nobomi/Arduino-ARMSID-configurator/Arduino/ARMSID_test/ARMSID_test.ino

/*
** ArmSID & Arm2SID tester/configurator using cc65 or Borland Turbo C++ V1.0. or Arduino and others
**
** Copyright (c) 2021 nobomi (Bohumil Novacek, dzin@post.cz)
**
** MIT License
**
** Permission is hereby granted, free of charge, to any person obtaining a copy
** of this software and associated documentation files (the "Software"), to deal
** in the Software without restriction, including without limitation the rights
** to use, copy, modify, merge, publish, distribute, sublicense, and/or sell
** copies of the Software, and to permit persons to whom the Software is
** furnished to do so, subject to the following conditions:
**
** The above copyright notice and this permission notice shall be included in all
** copies or substantial portions of the Software.
**
** THE SOFTWARE IS PROVIDED "AS IS", WITHOUT WARRANTY OF ANY KIND, EXPRESS OR
** IMPLIED, INCLUDING BUT NOT LIMITED TO THE WARRANTIES OF MERCHANTABILITY,
** FITNESS FOR A PARTICULAR PURPOSE AND NONINFRINGEMENT. IN NO EVENT SHALL THE
** AUTHORS OR COPYRIGHT HOLDERS BE LIABLE FOR ANY CLAIM, DAMAGES OR OTHER
** LIABILITY, WHETHER IN AN ACTION OF CONTRACT, TORT OR OTHERWISE, ARISING FROM,
** OUT OF OR IN CONNECTION WITH THE SOFTWARE OR THE USE OR OTHER DEALINGS IN THE
** SOFTWARE.
*/

#include "sidapi.h"

/*****************************************************************************/
/*                                   Data                                    */
/*****************************************************************************/

#ifdef ARM2SID
#define Nadpis "\\\\       nobomi armsid tester v3.16\\\\\\"
#else
#define Nadpis "\\\\       nobomi armsid tester v2.16\\\\\\"
#endif
#define Notfou "armsid not found"
#ifdef ARM2SID
#define Founda_0 "armsid"
#define Founda_1 "arm2sid  left channel"
#define Founda_2 "arm2sid right channel"
#else
#define Founda "armsid"
#endif

#define WarnBL      "!! warning ! bootloader fw  ! warning !!"
#define WarnBeta "!! warning ! beta firmware  ! warning !!"

/*****************************************************************************/
/*                                   Code                                    */
/*****************************************************************************/

static unsigned char SIDi;
static unsigned char version;
static unsigned char revision;
static unsigned char release;

struct s_vyber_list {
  const unsigned char left;
  const unsigned char top;
  const signed char rozsah;
};

typedef struct {
  unsigned char *vyber;
  const struct s_vyber_list *list;
  signed char *value;
} t_vyber;

static unsigned char vyber;
static unsigned char vyber_max;
signed char vyber_value[5];
signed char vyber_mask=0;
static const struct s_vyber_list extend_lists[4]={
  {0,4,7},
  {0,8,1},
  {0,12,3},
  {0,16,3}
};

#ifdef DIGIFIX
#define audio_value vyber_value
static const struct s_vyber_list audio_lists[2]={
  {0,9,0},
  {0,14,4},
};
static signed char audio_mem[4];
static unsigned char isext;
#endif

#ifdef ARM2SID
static unsigned char mem_value[8];
static unsigned char isARM2;
static unsigned char mem_emul;
static unsigned char ntsc;
static unsigned char downM;
static unsigned char socket;

#define EMUL_SID    0
#define EMUL_SFX    1
#define EMUL_SFX_SID  2

#define ADDR_MAP_NONE   0
#define ADDR_MAP_SIDL   1
#define ADDR_MAP_SIDR   2
#define ADDR_MAP_SFX    3
#define ADDR_MAP_SIDM   4

#define ADDR_MAP_D400   0
#define ADDR_MAP_D420   1
#define ADDR_MAP_D500   2
#define ADDR_MAP_D520   3
#define ADDR_MAP_DE00   4
#define ADDR_MAP_DE20   5
#define ADDR_MAP_DF00   6
#define ADDR_MAP_DF20   7
#endif

#define EXTIN_NO      0
#define EXTIN_YES     CHAR_E

#define DIGIFIX_NO        0
#define DIGIFIX_YES        0x58

char get_p(void) {
  return SIDrd(27);
}

char get_q(void) {
  return SIDrd(28);
}

//sending command
void send_cmd(char x31, char x30) {
  SIDwr(31, x31);
  SIDwr(30, x30);
}

//plus wait 10ms
void send_cmd_wait(char x31, char x30) {
  send_cmd(x31,x30);
  delay(10);
}

//sending config command and reading half of the two-byte output
char get_pcmd(char x31, char x30) {
  send_cmd(x31,x30);
  delay(1);
  return get_p();
}

//close the config mode
void sid_off(void) {
  SIDwr(29, 0);
  SIDwr(29, 0);
  SIDwr(29, 0);
}

//open the config mode
void sidoffon(void) {
  sid_off();
  delay(10);
  send_cmd(CHAR_D, CHAR_I);
  SIDwr(29, CHAR_S);
  delay(1);
}

void textcolorLB(void) {
  textcolor(COLOR_LIGHTBLUE);
}

void textcolorW(void) {
  textcolor(COLOR_WHITE);
}

//print char as a decimal
void cputbval(unsigned char x) {
  char sto=0;
  char deset=0;
  if (x>=100) {
    do {
      x-=100;sto++;
    } while (x>=100);
    cputc(sto+'0');
  }
  while (x>=10) {
    x-=10;deset++;
  }
  if (sto|deset) cputc(deset+'0');
  cputc(x+'0');
}

//print short as a 1/1000 decimal
void cput1000(unsigned short x) {
  char t=0;
  char m;
  while (x>=1000) {
    x-=1000;t++;
  }
  cputbval(t);
  cputc('.');
  t='0';while (x>=100) { x-=100;t++; } cputc(t);
  m=x;
  t='0';while (m>=10) { m-=10;t++; } cputc(t);
  cputc(m+'0');
}

//drawing acceleration, x,y = position, znak=character, kolik=number of characters, if negative then characters are in a column
struct s_canvas {
  unsigned char x;
  unsigned char y;
  unsigned char znak;
  signed char kolik;
} t_canvas;

//frame clearing
static const struct s_canvas prazdny_ramecek[]={
  {0,0,' ',40},
  {0,1,' ',-3},
  {39,1,' ',-3},
  {0,4,' ',40},
  {0,0,0,0}
};

//frame
static const struct s_canvas plny_ramecek[]={
// PC double lines
  {0, 0,  CHAR_FRAME_TOP_LEFT,      1 },
  {1, 0,  CHAR_FRAME_TOP,           38},
  {39,0,  CHAR_FRAME_TOP_RIGHT,     1 },
  {0, 1,  CHAR_FRAME_LEFT,          -3},
  {39,1,  CHAR_FRAME_RIGHT,         -3},
  {0, 4,  CHAR_FRAME_BOTTOM_LEFT,   1 },
  {1, 4,  CHAR_FRAME_BOTTOM,        38},
  {39,4,  CHAR_FRAME_BOTTOM_RIGHT,  1 },
  {0, 0,  0,                        0 }
};

//one line
static const struct s_canvas lajna[]={
  {2,2,CHAR_LINE,36},
  {0,0,0,0}
};

//automaton for drawing acceleration structures, x0,y0 = position offset
void namaluj(unsigned char x0, unsigned char y0, const struct s_canvas *c) {
  while (c->znak) {
    signed char i=c->kolik;
    if (i<0) {
      while (++i<=0) {
        gotoxy(x0+c->x,y0+c->y-i);
        cputc(c->znak);
      }
    } else {
      gotoxy(x0+c->x,y0+c->y);
      while (i) { cputc(c->znak);i--; }
    }
    c++;
  }
}

void candidate() {
    if (release) {
        char x=wherex();
        char y=wherey();
    (void) bordercolor(COLOR_YELLOW);
    (void) textcolor(COLOR_YELLOW);
        revers(1);
        if (release==255) {
            cputs2xy(0,0,WarnBL);
#ifdef TERMINAL_HEIGHT
      cputs2xy(0,TERMINAL_HEIGHT-1,WarnBL);
#else
      cputs2xy(0,24,WarnBL);
#endif
        } else {
      cputs2xy(0,0,WarnBeta);
#ifdef TERMINAL_HEIGHT
      cputs2xy(0,TERMINAL_HEIGHT-1,WarnBeta);
#else
      cputs2xy(0,24,WarnBeta);
#endif
        }
        revers(0);
        //back
    (void) textcolor(COLOR_WHITE);
        gotoxy(x,y);
    }
}

void new_page(void) {
    clrscr();
    candidate();
    cputs2(Nadpis);
}

//print the first page header
void uvod(void) {
    (void) textcolor(COLOR_WHITE);
    (void) bordercolor(COLOR_LIGHTBLUE);
    (void) bgcolor(COLOR_BLUE);
    new_page();
}

//filter setting key reaction
signed char vyber_zmena(const struct s_vyber_list *v, unsigned char key, char ramecek) {
  signed char res=-1;
    if ((key==17)||(key==17+128)) {
    namaluj(v[vyber].left,v[vyber].top,prazdny_ramecek);
    }
    switch (key) {
  case 17:
    //down
    vyber++;if (vyber>=vyber_max) vyber=0;
    break;
  case 17+128:
    //up
    if (vyber>0) vyber--;
    else vyber=vyber_max-1;
    break;
  case 29:
    //right
    if (v[vyber].rozsah) { if (vyber_value[vyber]<v[vyber].rozsah) { vyber_value[vyber]++;res=vyber; }
    } else { vyber_value[vyber]=1; res=vyber; }
    break;
  case 29+128:
    //left
    if (v[vyber].rozsah) { if (vyber_value[vyber]>-v[vyber].rozsah) { vyber_value[vyber]--;res=vyber; }
    } else { vyber_value[vyber]=0;res=vyber; }
    break;
  default:
  break;
    }
    if ((v[vyber].rozsah)&&((vyber_value[vyber]>v[vyber].rozsah)||(vyber_value[vyber]<-v[vyber].rozsah))) { vyber_value[vyber]=0;res=vyber; }
    if (((key==17)||(key==17+128))&&(ramecek)) {
    namaluj(v[vyber].left,v[vyber].top,plny_ramecek);
    }
  namaluj(v[vyber].left,v[vyber].top,lajna);
  if (v[vyber].rozsah) {
      gotoxy(v[vyber].left+19+((17*vyber_value[vyber])/v[vyber].rozsah),v[vyber].top+2);
  } else {
    gotoxy(v[vyber].left+2+34*(vyber_value[vyber]&1),v[vyber].top+2);
  }
    cputc(CHAR_CHOICE_1);
    cputc(CHAR_CHOICE_2);
  return res;
}

//print extended page offer
void save_back_quit(void) {
#ifdef TERMINAL_HEIGHT
  gotoxy(4,TERMINAL_HEIGHT-2);
#else
  gotoxy(4,22);
#endif
  cputs2("@save / @permanently / @back / @quit");
}

//print the filter setting page
void uvod_extend(void) {
    uvod();

    cputs2xy(0+8, 4+1,       "mos 6581 filter strength");

    cputs2xy(0+1, 4+3,"follin galway  average  strong extreme");

    cputs2xy(0+4, 8+1,   "mos 6581 lowest filter frequency");

    cputs2xy(0+1, 8+3," 150             215              310");

    cputs2xy(0+4,12+1,   "mos 8580 filter central frequency");

    cputs2xy(0+1,12+3," 12000           6000            3000");

    cputs2xy(0+4,16+1,   "mos 8580 lowest filter frequency");

    cputs2xy(0+1,16+3," 30              100              330");

    save_back_quit();

    vyber=0;
    vyber_zmena(extend_lists,17,0);
    vyber_zmena(extend_lists,17,0);
    vyber_zmena(extend_lists,17,0);
    vyber_zmena(extend_lists,17,1);
}

//print nibble as a hex value
void cputnibble(unsigned char x) {
  x&=15;
  if(x>9) x=('a'-10)+x;
  else x+='0';
  cputc(x);
}

//print short as a hex value
void cputhex_mem(unsigned short x) {
  cputc('$');
  cputnibble(x>>12);
  cputnibble(x>>8);
  cputnibble(x>>4);
  cputnibble(x);
}

#ifdef SOCKETS_NAMED
void cputhex(unsigned short x) {
  cputs2("socket ");
  if (x&0x3FF) cputc('2');
  else cputc('1');
}
#else
void cputhex(unsigned short x) {
  cputhex_mem(x);
}
#endif

//saving configuration to the ram or permanently to the flash memory of ARMSID
void save(char jak) {
    char i;
    clrscr();
    uvod();
    switch(jak) {
  case 's':
      gotoxy(13,12);
      cputs2("saving to ram");
    send_cmd(0xC0,CHAR_E);
      gotoxy(13,13);
      for(i=0;i<13;i++) {
    delay(1000/13);
    cputc('#');
      }
  break;
  case 'p':
      gotoxy(12,12);
      cputs2("saving to flash");
    send_cmd(0xCF,CHAR_E);
      gotoxy(12,13);
      for(i=0;i<15;i++) {
    delay(2000/15);
    cputc('#');
      }
  break;
  default:break;
    }
}

#ifdef ARM2SID
//update memory mapping page with item x highlighted
void vyber_mem(char x) {
  char i;
  char is3=((mem_value[1]==ADDR_MAP_SIDM)||(mem_value[2]==ADDR_MAP_SIDM))&&(!socket);
  for(i=0;i<8;i++) {
      gotoxy(5+((i>>2)?18:0),8+((i&3)<<1));
      if (socket) {
      if (i&3) textcolor(COLOR_BLUE);
      if (i&4) cputs2("sid/2:");
      else cputs2("sid/1:");
      textcolorW();
    } else {
      cputhex_mem((int)SIDgetaddr(i));
      cputc(':');
    }
  }
  for(i=0;i<8;i++) {
      gotoxy(5+7+((i>>2)?18:0),8+((i&3)<<1));
      if (x==i) revers(1);
      if (socket) {
      if (i&3) {
        textcolor(COLOR_BLUE);
        cputs2("none");
        goto vyber_dalsi;
      }
    }
    if ((mem_emul==EMUL_SFX_SID)&&(i<(socket?4:6))) {
      if (i==0) {
        cputs2("sidl");
      } else {
        cputs2("Lnone");
      }
    } else if ((i>=(socket?4:6))&&(mem_emul>=EMUL_SFX)) cputs2("sfx ");
      else switch (mem_value[i]) {
      case ADDR_MAP_SFX:
        if (mem_emul==EMUL_SFX) textcolorLB();
        cputs2("sfx ");
        break;
      case ADDR_MAP_SIDL:
        if (mem_emul==EMUL_SFX) textcolorLB();
        cputs2("sidl");
        break;
      case ADDR_MAP_SIDR:
        if (mem_emul==EMUL_SFX) textcolorLB();
        if ((mem_emul==EMUL_SID)||(i>0)) cputs2("sidr");
        else cputs2("sidl");
        break;
      case ADDR_MAP_SIDM:
        if (mem_emul==EMUL_SFX) textcolorLB();
        else if (mem_emul==EMUL_SID) textcolor(COLOR_LIGHTGREEN);
        if ((mem_emul==EMUL_SID)||(i>0)) cputs2("sid3");
        else cputs2("sidl");
        break;
      case ADDR_MAP_NONE:
      default:
          if (x!=i) textcolorLB();
        cputs2("none");
        break;
    }
vyber_dalsi:
    textcolorW();
      if (x==i) revers(0);
  }
    gotoxy(4+18,16);
  if (!is3) cputc(' ');
  textcolorLB();
  if (mem_emul==EMUL_SFX_SID) {
    if (is3) { cputc(' '); }
    cputs2("sid sfx ");
    if (x==8) revers(1);
    cputs2("WbothR");
  } else if (mem_emul==EMUL_SFX) {
    if (is3) { cputc(' '); }
    cputs2("sid ");
    if (x==8) revers(1);
    cputs2("WsfxR LbothW");
  } else {
    if (x==8) revers(1);
    if (is3) { textcolor(COLOR_LIGHTGREEN);cputc('3'); }
    cputs2("WsidR Lsfx bothW");
  }
  //pal ntsc
  gotoxy(5+18,18);
  if (mem_emul==EMUL_SID) {
    cputs2("Lpal ntscW");
  } else {
    if (ntsc) {
      cputs2("Lpal W");
      if (x==9) revers(1);
      cputs2("ntscR");
    } else {
      if (x==9) revers(1);
      cputs2("palRL ntscW");
    }
  }
  //mono
  gotoxy(5+18,20);
  if (mem_emul==EMUL_SFX) {
    cputs2("Loff onW");
  } else {
    if (downM) {
      cputs2("Loff W");
      if (x==10) revers(1);
      cputs2("onR");
    } else {
      if (x==10) revers(1);
      cputs2("offRL onW");
    }
  }
  //socket
  gotoxy(5+18,6);
    if (socket) {
      cputs2("Lwire W");
      if (x==11) revers(1);
      cputs2("socketR");
    } else {
      if (x==11) revers(1);
      cputs2("wireRL socketW");
    }
}

static const char socket_next[12]={0,4,2,0,4,8,6,4,8,9,10,11};

//memory mapping key reaction
void mem_zmena(unsigned char key) {
  char vyber_old=vyber;
    switch (key) {
  case 17:
    //down
    vyber++;if (vyber>11) vyber=0;
    if ((vyber==9)&&(mem_emul==0)) vyber=10;
    if ((vyber==10)&&(mem_emul==1)) vyber=11;
    if ((mem_emul>=EMUL_SFX)&&(vyber<8)) vyber=8;
    break;
  case 17+128:
    //up
    if (vyber>0) vyber--;
    else vyber=11;
    if ((mem_emul>=EMUL_SFX)&&(vyber<8)) vyber=11;
    if ((vyber==10)&&(mem_emul==1)) vyber=9;
    if ((vyber==9)&&(mem_emul==0)) vyber=8;
    break;
  case 29:
    //right
    if (vyber==11) {
      socket^=1;
    } else if (vyber==10) {
      downM^=1;
    } else if (vyber==9) {
      ntsc^=4;
    } else if (vyber==8) {
      mem_emul++;//=(mem_emul+1)%3;
      if (mem_emul>=3) mem_emul=0;
    } else {
      mem_value[vyber]++;
      if (mem_value[vyber]>4) mem_value[vyber]=0;
      else if (mem_value[vyber]>2) {
        if (vyber==0) mem_value[vyber]=1;
        else {
          if ((vyber==1)||(vyber==2)) mem_value[vyber]=4; //enable for D420 a D500
          else mem_value[vyber]=0;
        }
      }
    }
    break;
  case 29+128:
    //left
    if (vyber==11) {
      socket^=1;
    } else if (vyber==10) {
      downM^=1;
    } else if (vyber==9) {
      ntsc^=4;
    } else if (vyber==8) {
      mem_emul+=2;
      if (mem_emul>=3) mem_emul-=3;
    }
    else {
      if (mem_value[vyber]==0) {
        if ((vyber==0)||(vyber>2)) mem_value[vyber]=2;  //povolit jen pro D420 a D500
        else mem_value[vyber]=4;
      }
      else if (mem_value[vyber]==4) mem_value[vyber]=2;
      else mem_value[vyber]--;
      if ((vyber==0)&&(mem_value[vyber]==0)) mem_value[vyber]=2;
    }
    break;
  default:
  break;
    }
    if (vyber_old!=vyber) {
    vyber_mem(-1);
    if (socket) vyber=socket_next[vyber];
  }
    vyber_mem(vyber);
}

//print memory mapping page
void uvod_mem(void) {
    uvod();
    gotoxy(5,3);
    cputs2("address mapping configuration");
    gotoxy(5,6);
    cputs2("pin connections:");
    gotoxy(5,16);
    cputs2("emulation mode: ");
    gotoxy(5,18);
    cputs2("fm frequency ref:");
    gotoxy(5,20);
    cputs2("down-mix to mono:");
  save_back_quit();
  vyber=8;
  vyber_mem(vyber);
}

//memory mapping reading
void nacti_mem(void) {
    unsigned char p,q;
  p=get_pcmd(CHAR_M,CHAR_M);
    q=get_q();
    mem_emul=p&7;
    if (mem_emul&4) ntsc=4; else ntsc=0;
    if ((mem_emul&3)==3) mem_emul=1;
    mem_emul&=3;
  p=get_pcmd(CHAR_X,CHAR_M);
    q=get_q();
    downM=p&1;
    socket=q&1;
    delay(10);
  p=get_pcmd(CHAR_L,CHAR_M);
    q=get_q();
    mem_value[0]=p&15;
    mem_value[1]=p>>4;
    mem_value[2]=q&15;
    mem_value[3]=q>>4;
    delay(10);
  p=get_pcmd(CHAR_H,CHAR_M);
    q=get_q();
    mem_value[4]=p&15;
    mem_value[5]=p>>4;
    mem_value[6]=q&15;
    mem_value[7]=q>>4;
#ifdef DEMO
  mem_value[0]=1;
  mem_value[1]=2;
  mem_value[2]=2;
  mem_value[3]=1;
  mem_value[4]=0;
  mem_value[5]=0;
  mem_value[6]=0;
  mem_value[7]=0;
  ntsc=0;
  socket=0;
  mem_emul=0;
  downM=0;
#endif
}

//memory mapping page automaton
char mem(void) {
    unsigned char key;
    uvod_mem();
    while (1) {
      if (keypressed()) {
      key=cgetc();
      if ((key=='q')||(key=='b')) return key;
      if ((key=='s')||(key=='p')) {
        send_cmd_wait('0'+(mem_emul)+((mem_emul)?(ntsc):0),CHAR_M);
        send_cmd_wait(((downM)?CHAR_R:CHAR_S),CHAR_M);
        send_cmd_wait(((socket)?CHAR_E:CHAR_C),CHAR_M);
        {
          unsigned char i=0;
          while (i<8) {
            send_cmd_wait(0x80|(i<<4)|(mem_value[i]&15),CHAR_M);
            i++;
          }
        }
      }
      if (key=='s') {
      save(key);
      return 'r';
      }
      if (key=='p') {
      save(key);
      return 'r';
      }
        mem_zmena(key);
    }
    }
}

//ARM2SID testing => if answer to command "SII" is L or R then it's ARM2SID otherwise it's ARMSID
char test_lr(char x) {
#ifdef DEMO
  SIDaddr=(SIDaddrtype)(SIDgetaddr(x));SIDi=x;
  isARM2=1;return (x+1)%3;
#else
  unsigned char p,q;
  char res=0;
  isARM2=0;
  SIDaddr=(SIDaddrtype)(SIDgetaddr(x));SIDi=x;
  sidoffon();
  p=get_pcmd(CHAR_I,CHAR_I);
  q=get_q();
  if (p!=2) res=0;    //neni ARM2
  else if (q==CHAR_L) { res=1;isARM2=1; } //je levy kanal
  else if (q==CHAR_R) { res=2;isARM2=1; } //je pravy kanal
  sid_off();
  return res;
#endif
}

void printf_sid(char sid, int addr) {
  switch (test_lr(sid)) {
    case 1: cputs2(Founda_1); break;
    case 2: cputs2(Founda_2); break;
    default: cputs2(Founda_0); break;
  }
  cputs2(" found at ");cputhex(addr);cputs2("\\");
}

void printf_sidi(void) {
  printf_sid(SIDi,(int)SIDaddr);
}

void printf_found(char n, char sid) {
  cputc(n+'0');cputs2(") ");printf_sid(sid,(int)SIDgetaddr(sid));
}

#else //ARM2SID

void printf_sid(int addr) {
  cputs2(Founda);cputs2(" found at ");cputhex(addr);cputs2("\\");
}

void printf_sidi(void) {
  printf_sid((int)SIDaddr);
}

void printf_found(char n, char sid) {
  cputc(n+'0');cputs2(") ");printf_sid((int)SIDgetaddr(sid));
}

#endif //ARM2SID

signed char vyber_sid(char i) {
  signed char res=0;
  char id[3];
  char n=0;
  char a;
  int x;
  char s[4];
  cputs2("more than one armsid found !\\\\");
  for (x=0;x<SIDaddresses;x++) {
    if (i&(1<<x)) {
      id[n++]=x+1;
      printf_found(n,x);
    }
  }
  cputs2("\\press ");
  s[0]='@';
  s[2]=',';
  s[3]=0;
  for (x=0;x<n-2;x++) {
    s[1]='1'+x;
  	cputs2_var(s);
  }
  s[2]=0;
  if (x<n-1) {
	s[1]='1'+x++;
  	cputs2_var(s);
  }
  cputs2(" or ");
  s[1]='1'+x;
  cputs2_var(s);
  cputs2(" to choose one\\or press @q to quit\\");
  while (1) {
      if (keypressed()) {
    a=cgetc();
    if (a=='q') { res=-1; break; }
    if ((a>='0')&&(a<='9')) {
        a=a-'1';
        if (a<n) {
          res=id[a];
          SIDaddr=(SIDaddrtype)(SIDgetaddr(res-1));SIDi=res-1;
          break;
        }
      }
    }
  }
  return res;
}

void najdi2(void) {
  printf_sidi();
  sidoffon();
}

//ARMSID search
signed char najdi(void) {
  int res=(1<<SIDaddresses)-1;  // all in
#ifdef DEMO
  res=5;
#ifdef ARM2SID
  res=3;
#endif
#else
  int i,j;
  unsigned char p,q;
  unsigned char first=1;
  SIDi=0;
  // mute all
  for (i=0;i<SIDaddresses;i++) {
    SIDaddr=SIDgetaddr(i);
    SIDwr(24,0);  //silent
    SIDwr(24,0);
    SIDwr(24,0);
    sid_off();
  }
  // test all addresses
  for (i=0;i<SIDaddresses;i++) {
    SIDaddr=SIDgetaddr(i);
    if (res&(1<<i)) {
      sidoffon();
      p=get_p();
      q=get_q();
      if ((p!=CHAR_N)||(q!=CHAR_O)) {
        res^=(1<<i); // not the one
        sid_off();
        continue;
      }
      p=get_pcmd(CHAR_E,CHAR_I);
      q=get_q();
      if ((p!=CHAR_S)||(q!=CHAR_W)) {
        res^=(1<<i); // not the one
        sid_off();
        continue;
      }
    }
    // now looking for a duplicate
    for (j=i+1;j<SIDaddresses;j++) {
      SIDaddr=SIDgetaddr(j);
      p=get_pcmd(CHAR_D,CHAR_I);
      q=get_q();
      if ((p!=CHAR_N)||(q!=CHAR_O)) continue;
      p=get_pcmd(CHAR_E,CHAR_I);
      q=get_q();
      if ((p!=CHAR_S)||(q!=CHAR_W)) continue;
      res^=(1<<j); // duplicated
    }
    SIDaddr=SIDgetaddr(i);
    sid_off();
    if (first==1) {
      SIDi=i; // remember first working
      first=0;
    }
  }
#endif
  if (res&(res-1)) res=vyber_sid(res);
  else { // just one
    SIDaddr=SIDgetaddr(SIDi);
  }
  if (res==0) {
    cputs2(Notfou);
    cputs2("\\");
  }
  return res;
}

#ifdef UID
void cputascii(unsigned char c) {
  if ((c<=0x20)||(c>=128)) c='/';
  cputc(c);
}
#endif

//details printing
void details(void) {
  unsigned char p,q;
  p=get_pcmd(CHAR_V,CHAR_I);
  q=get_q();
#ifdef DEMO
  p=2;
  q=16;
#ifdef ARM2SID
  p=3;
#endif
#endif
  version=p;
  revision=q;
  cputs2("fw version:");
  cputbval(p);
  cputc('.');
  cputbval(q);
  p=get_pcmd(CHAR_R,CHAR_I);
#ifdef DEMO
  p='0';
#endif
  if ((p>'0')&&(p<CHAR_E)) {
    release=p-'0';
    cputs2(" beta ");
    cputbval(release);
  }
  cputs2("\\");

  p=get_pcmd(CHAR_F,CHAR_I);

  if ((p<=32)||(p>127)) p='.';
  q=get_q();if ((q<=32)||(q>127)) q='.';
#ifdef DEMO
  p='8';
  q='5';
#endif
  if (version>=2) {
    cputs2("emulated device:");
    cputc(p);
    cputc(q);
    cputs2("xx");
    p=get_pcmd(CHAR_G,CHAR_I);
    if (p=='7') cputs2("(auto detected)\\");
    else cputs2("               \\");
    } else {
    cputs2("emulated device:");
    cputc(p);
    cputc(q);
    cputs2("xx\\");
  }
  p=get_pcmd(CHAR_I,CHAR_F);
  if ((p<=32)||(p>127)) p='.';
  q=get_q();if ((q<=32)||(q>127)) q='.';
#ifdef DEMO
  p='a';
  q='p';
#endif
  cputs2("app/boot:");
  cputc(p);
  cputc(q);
  if ((p==CHAR_B)&&(q==CHAR_L)) release=255;
  cputs2("\\");
#ifdef DEMO
  {
    unsigned char ii;
    cputs2("s/n:");
    cputascii('q');
    for (ii=0xC4;ii<=0xC6;ii++) {
      cputascii('1');
      cputascii('2');
    }
    cputc('/');
    cputbval(23);
    cputc('/');
    q=1;p=34;
    if (q>0) cputascii(q+0x40);
    cputbval(p);
    cputc('/');
    q=1;p=45;
    if (q>0) cputascii(q+0x40);
    cputbval(p);
  }
#else
#ifdef UID
  p=get_pcmd(0xC0,CHAR_I);q=get_q();
  if ((p==0x55) && (q==0x49)) { // UI
    unsigned char ii;
    cputs2("s/n:");
    p=get_pcmd(0xC3,CHAR_I);
    q=get_q();
    cputascii(q);
    for (ii=0xC4;ii<=0xC6;ii++) {
      p=get_pcmd(ii,CHAR_I);
      q=get_q();
      cputascii(p);
      cputascii(q);
    }
    cputc('/');
    p=get_pcmd(0xC3,CHAR_I);
    cputbval(p);
    cputc('/');
    p=get_pcmd(0xC1,CHAR_I);
    q=get_q();
    if (q>0) cputascii(q+0x40);
    cputbval(p);
    cputc('/');
    p=get_pcmd(0xC2,CHAR_I);
    q=get_q();
    if (q>0) cputascii(q+0x40);
    cputbval(p);
  }
#endif
#endif
#ifdef DIGIFIX
#ifdef DEMO
  isext=1;
#else
  isext=0;
  p=get_pcmd(0x64,CHAR_I);
  q=get_q();
  if ((p==0x64)&&((q==DIGIFIX_NO)||(q==DIGIFIX_YES))) isext=1;
#endif
#endif
  cputs2("\\\\\\\\\\\\press ");
  cputs2("@6/@7/@8 to 6581/auto/8580 emulation\\press ");
  if (version>=2) {
    cputs2("@p to permanently save\\press @e to extended (filter) menu ...\\press ");
    if (revision>=13) {
      cputs2("@x to extra features menu ...\\press ");
    }
  }
#ifdef DIGIFIX
  if (isext) {
    cputs2("@d to mos8580 digifix settings ...\\press ");
  }
#endif
#ifdef ARM2SID
  if (isARM2) {
    cputs2("@m to address mapping configurationpress ");
  }
#endif
  cputs2("@r to restart the tester\\and @q to quit\\");
  if (version>=2) {
  } else {
    cputs2("  upgrade firmware to version 2.0 and\\      newer for new features !!!\\");
  }
  gotoy(11);
  if (release) candidate();
}

void fillx(unsigned char x)
{
  signed char n=x-wherex();
  while(n-->0) cputc(' ');
}

#ifdef DEMO
static char napeti_zmena=0;
#define napeti  9123
#endif

//analog values test
void analog(void) {
  unsigned char x,y,mem;
  short v;
  mem=wherey();
  x=SIDrd(25);
  y=SIDrd(26);
  cputs2("potx=");
  cputbval(x);fillx(15);
  cputs2("\\poty=");
  cputbval(y);fillx(15);
  ((char*)&v)[1]=get_pcmd(CHAR_U,CHAR_I);
  ((char*)&v)[0]=get_q();
#ifdef DEMO
  x=101;
  y=255;
  ((char*)&v)[1]=napeti/256;
  ((char*)&v)[0]=napeti%256;
  napeti_zmena^=1;
  if (napeti_zmena) napeti_zmena-=1;
#endif
  cputs2("\\vdd=");
  cput1000(v);
  cputs2(" v");fillx(15);
#ifdef ARM2SID
  ((char*)&v)[1]=get_pcmd(CHAR_T+0x20,CHAR_I);
  ((char*)&v)[0]=get_q();
#ifdef DEMO
  v=255;
#endif
  if (v!=0x4552) {
    cputs2("Lt=");
    if (v<0) {
      cputc('-');
      v=0-v;
    }
    cputbval(v/10);
    cputc('.');
    cputbval(v%10);
    cputc(CHAR_DEGREE);
    cputs2("cW     ");
  }
#endif
  gotoxy(0,mem);
}

//filter setting reading
void nacti_extend(void) {
  unsigned char p,q;
  signed char v;
  vyber_max=4;
  p=get_pcmd(CHAR_H,CHAR_I);
  q=get_q();
  v=p;
  v=v>>4;
  vyber_value[0]=v;
  v=p<<4;
  v=v>>4;
  vyber_value[1]=v;
  v=q;
  v=v>>4;
  vyber_value[2]=v;
  v=q<<4;
  v=v>>4;
  vyber_value[3]=v;
}

//extended page (filter setting) automaton
char extended(void) {
  unsigned char key;
  uvod_extend();
  while (1) {
    if (keypressed()) {
      key=cgetc();
      if ((key=='q')||(key=='b')) return key;
      if ((key=='s')||(key=='p')) {
        unsigned char i=0;
        while (i<4) {
          send_cmd_wait(0x80|(i<<4)|(vyber_value[i]&15),CHAR_E);
          i++;
        }
        save(key);
        return 0;
      }
      vyber_zmena(extend_lists,key,1);
    }
  }
}

char is_extra() {
#ifdef ARM2SID
    if ((version==3)&&(revision>=16)) return 1|2|4|8|16;
    if ((version==3)&&(revision>=14)) return 1|2|4;
#endif
    if ((version==2)&&(revision>=16)) return 2|8|16;
	return 2;
}

void vyber_extra(unsigned char key) {
  gotoxy(32,7+vyber*2);
  if (((1<<vyber)&vyber_mask)!=0) {
	if (vyber_value[vyber]&1) cputs2("yes");
    else cputs2("no ");
  }
  switch (key) {
    case 17:
      //down
      if (vyber_mask!=0) do {
        ++vyber;
        if (vyber>=5) vyber=0;
      } while (((1<<vyber)&vyber_mask)==0);
      break;
    case 17+128:
      //up
      if (vyber_mask!=0) do {
        if (vyber==0) vyber=5-1;
        else --vyber;
      } while (((1<<vyber)&vyber_mask)==0);
      break;
    case 29:
      //right
      //break;
    case 29+128:
      //left
      vyber_value[vyber]^=3;
      break;
    default: break;
  }
  gotoxy(31,7+vyber*2);
  if (vyber_value[vyber]&2) cputs2("L*W");
  else cputs2(" ");
  revers(1);
  if (vyber_value[vyber]&1) cputs2("yesR");
  else cputs2("noR ");
}

//print extra setting page
void uvod_extra(void) {
  uvod();
  gotoxy(6,3);
  cputs2("extra features settings menu");
  vyber=5-1;
  if ((vyber_mask&1)!=0) {
	gotoxy(6,7);
	cputs2("auto mono to stereo off:  ");
	if (vyber_value[0]&1) cputs2("yes");
	else cputs2("no");
  }
  if ((vyber_mask&2)!=0) {
    gotoxy(6,9);
    cputs2("original adsr bug fixed:  ");
    if (vyber_value[1]&1) cputs2("yes");
    else cputs2("no");
  }
  if ((vyber_mask&4)!=0) {
	gotoxy(6,11);
	cputs2("duplicate left to right:  ");
	if (vyber_value[2]&1) cputs2("yes");
	else cputs2("no");
  }
  if ((vyber_mask&8)!=0) {
	gotoxy(5,13);
//	cputs2("auto vdd threshold 2 volts:  ");
	cputs2("low autodetect threshold:  ");
	if (vyber_value[3]&1) cputs2("yes");
	else cputs2("no");
  }
  if ((vyber_mask&16)!=0) {
	gotoxy(3,15);
	cputs2("ext in mixed to the filter:  ");
	if (vyber_value[4]&1) cputs2("yes");
	else cputs2("no");
	vyber=0;
  }
/*  gotoxy(6,9);
  cputs2("original adsr bug fixed:  ");
  if (vyber_value[1]&1) cputs2("yes");
  else cputs2("no");*/
  save_back_quit();
  vyber_extra(17);
}

//extra setting reading
void nacti_extra(void) {
  unsigned char p,q;
  vyber_mask=is_extra();
  if ((vyber_mask&5) != 0) {
	p=get_pcmd(CHAR_M,CHAR_M);
    q=get_q();
    vyber_value[0]=0;
    vyber_value[2]=0;
    if ((p!=CHAR_E)&&(q&0x40)) vyber_value[0]=1;
    if ((p!=CHAR_E)&&(q&0x20)) vyber_value[2]=1;
  }
  if ((vyber_mask&8) != 0) {
	p=get_pcmd(0x39,CHAR_I);
    q=get_q();
    vyber_value[3]=0;
    if ((p==0x39)&&(q==CHAR_V)) vyber_value[3]=1;
  }
  if ((vyber_mask&16) != 0) {
	p=get_pcmd(CHAR_A,CHAR_I);
    q=get_q();
    vyber_value[4]=0;
    if ((p==CHAR_A)&&(q==CHAR_E)) vyber_value[4]=1;
  }
  p=get_pcmd(CHAR_O,CHAR_I);
  q=get_q();
  vyber_value[1]=0;
  if ((p==CHAR_O)&&(q==CHAR_F)) vyber_value[1]=1;
}

//extra page (non C64) automaton
char extra(void) {
  unsigned char key;
  uvod_extra();
  while (1) {
    if (keypressed()) {
      key=cgetc();
      if ((key=='q')||(key=='b')) return key;
      if ((key=='s')||(key=='p')) {
        unsigned char i;
		if ((vyber_mask&5) != 0) {
          i=CHAR_M;if (vyber_value[0]&1) i+=32;
          send_cmd_wait(i,CHAR_E);
          i=CHAR_N;if (vyber_value[2]&1) i+=32;
          send_cmd_wait(i,CHAR_E);
        }
		if ((vyber_mask&24) != 0) {
          i=0x30;if (vyber_value[3]&1) i=0x39;
          send_cmd_wait(i,CHAR_E);
          i=CHAR_B;if (vyber_value[4]&1) i+=32;
          send_cmd_wait(i,CHAR_A);
        }
        i=CHAR_O;if (vyber_value[1]&1) i+=32;
        send_cmd_wait(i,CHAR_E);
        save(key);
        return 0;
      }
      vyber_extra(key);
    }
  }
}

#ifdef DIGIFIX
void ping(unsigned char st) {
#ifdef C64_ONLY
static SIDaddrtype ping_sid;
#endif
  unsigned char n;
  unsigned char d;
  unsigned char x=0;
  if (audio_mem[2]==0) return;
  send_cmd_wait(st,CHAR_E);
  sid_off();
  SIDwr(23,7);
#ifdef C64_ONLY
  ping_sid=&SIDaddr[24];
  *ping_sid=0;
#else
  SIDwr(24,0);
#endif
  delay(70);
  d=15;
  while(d) {
    unsigned char up=1;
    n=100;
    while (n) {
      if (up&&(x<d)) ++x; else up=0;
      if (!up&&x) --x; else up=1;
#ifdef C64_ONLY
      *ping_sid=x;
#else
      SIDwr(24,x);
#endif
      --n;
    }
    --d;
  }
#ifdef C64_ONLY
  *ping_sid=0;
#else
  SIDwr(24,0);
#endif
  sidoffon();
  send_cmd_wait(audio_mem[3],CHAR_E);
}

void digifix_analog(void) {
#ifdef DEMO
    static short zz;
#endif
    short v,vv;
    short vref;
    gotoxy(2,5);
    ((char*)&vref)[1]=get_pcmd(CHAR_R+0x20,CHAR_I);
    ((char*)&vref)[0]=get_q();
#ifdef ARM2SID
    if (isARM2) {
#ifdef DEMO
        vref=3300;
#endif
        if (vref!=0x4552) {
            cputs2("Lref=");
            cput1000(vref);
            cputs2(" vW");
        } else vref=3300;
        fillx(16);
    }
#endif
    ((char*)&v)[1]=get_pcmd(CHAR_E+0x20,CHAR_I);
    ((char*)&v)[0]=get_q();
#ifdef DEMO
    vref=1623*2;
    v=zz;
        zz=1623;
#endif
    if (v!=0x4552) {
            vv=vref/2-v;
        cputs2("\\  vin=");
        if (v<0) {
            cputc('-');
            v=0-v;
        }
        cput1000(v);
        cputs2(" v    \\  iin=");
        v+=v;
        v=v-vref;
        v*=5;
        v/=4;    // *0.8
        v=v+v/128;
        if (v<0) {
            cputc('-');
            v=0-v;
        } else cputc('+');
        cputbval(v/100);
        v%=100;
        cputc('.');
        cputbval(v/10);
        cputbval(v%10);
        cputs2(" ua");
        fillx(16);
        gotoxy(32,14+6);
        vv*=12;
        vv/=41;
        if (vv>100) vv=100;
        if (vv<-100) vv=-100;
       if (vv<0) {
        cputc('-');
        vv=0-vv;
        }
        cputbval(vv);
        cputc('%');
    fillx(39);
    }
}

void nacti_digifix(void) {
    unsigned char p,q;
    signed char s;
    vyber_max=2;

    // audio in
    p=get_pcmd(0x64,CHAR_I);
       q=get_q();
       audio_value[0]=0;
    if ((p==0x64)&&(q==DIGIFIX_YES)) audio_value[0]=1;
    audio_mem[0]=audio_value[0];

    p=get_pcmd('8',CHAR_I);
       s=get_q()-128;
       audio_value[2]=4;
       s=s/8;
    if ((p=='d')&&(s>=-4)&&(s<=4)) audio_value[1]=s;
    audio_mem[1]=audio_value[1];

    // SID type
    p=get_pcmd('g',CHAR_I);
       s=get_q();
    if ((s=='5')&&(p>='6')&&(p<='8')) audio_mem[2]=p;
    else audio_mem[2]=0;
}

void lineupdate_digifix(void) {
    if (audio_value[0]) {
        textcolorW();
    } else {
        textcolorLB();
    }
    cputs2xy(3,14+1,  "mos 8580 software digifix strength");
    cputs2xy(1,14+3,"-100 -75 -50 -25  0%  25  50  75  100");
    if (audio_value[0]) {
        textcolorLB();
    } else {
        textcolorW();
    }
        cputs2xy(2,14+6,"digifix by ext. hardware pin: ");
    textcolorW();
}

void uvod_digifix(void) {
    uvod();
    cputs2xy(8,  3,       "digifix mos8580 settings");
    cputs2xy(9,9+1,        "digifix controlled by");
    cputs2xy(1,9+3," hardware                    software");
        lineupdate_digifix();

    save_back_quit();

    vyber=0;
    vyber_zmena(audio_lists,17,0);

    vyber_zmena(audio_lists,17,1);
}

//extended page (filter setting) automaton
unsigned char digifix(void) {
    unsigned char key,res;
    uvod_digifix();
    SIDwr(4,0);
    SIDwr(11,0);
    SIDwr(18,0);
    SIDwr(23,0);
    while (1) {

            vyber_max=audio_value[0]+1;

        if (keypressed()) {
            key=cgetc();
            SIDwr(24,0);
            if ((key=='q')||(key=='b')) {
                send_cmd_wait((audio_mem[0])?0x64:0x44,CHAR_A);
                send_cmd_wait((audio_mem[1]&0x0F)|0xB0,CHAR_A);

                return key;
            }
            if ((key=='s')||(key=='p')) {
                send_cmd_wait((audio_value[0])?0x64:0x44,CHAR_A);
                send_cmd_wait((audio_value[1]&0x0F)|0xB0,CHAR_A);

                save(key);
                return 0;
            }

            res=vyber_zmena(audio_lists,key,1);
            switch (res) {
                case 0:
                    send_cmd_wait((audio_value[0])?0x64:0x44,CHAR_A);
                    lineupdate_digifix();
                    break;
                case 1:
                    send_cmd_wait(0x64,'a');
                    send_cmd_wait((audio_value[1]&0x0F)|0xB0,CHAR_A);





                    ping('8');
                    break;
                default:
                    break;
            }
        } else {
            digifix_analog();
            delay(150);
        }
    }
}
#endif

////////////////////////////////////////////////////////////////////////////////

int main(main_params)
{
  signed char a=0;
  main_begin();
  while (a!='q') {
  release=0;
  uvod();
  a=najdi();
  if (a<=0) break; //return EXIT_SUCCESS;
  while ((a!='q')&&(a!='r')) {
    uvod();
    najdi2();
    details();
    while (1) {
    analog();
    if (keypressed()) {
        a=cgetc();
        if ((a=='q')||(a=='r')) {
      clrscr();
      gotoxy(1,1);
      break;
        }
        if ((a>='6')&&(a<='8')) {
      send_cmd_wait(a,CHAR_E);
      break;
        }
#ifdef ARM2SID
      if (isARM2) {
        if (a=='m') { //mem map cfg
          nacti_mem();
          a=mem();
          if (a=='q') {
            clrscr();
            gotoxy(1,1);
            break;
          }
          break;
        }
      }
#endif
#ifdef DIGIFIX
      if (isext) {
        if (a=='d') { //digifix
          clrscr();
          nacti_digifix();
          a=digifix();
          if (a=='q') {
            clrscr();
            gotoxy(1,1);
            break;
          }
          break;
        }
      }
#endif
        if (version>=2) {
          if (a=='p') {
            save('p');
            break;
          }
          if (a=='e') {
            nacti_extend();
            a=extended();
            if (a=='q') {
              clrscr();
              gotoxy(1,1);
              break;
            }
            a=0;
            break;
          }
          if (revision>=13) {
            if (a=='x') {
              nacti_extra();
              a=extra();
              if (a=='q') {
                clrscr();
                gotoxy(1,1);
                break;
              }
              a=0;
              break;
            }
          }
        }
    }
    delay(150);
      }
  }
  cputs2("\\\\\\\\\\\\");
  sid_off();
    }
  if (a==0) {
    main_nosid();
  }
  main_end();
  return EXIT_SUCCESS;
}
